fgebhart/smart_alarm/playground/light_up_leds.py

import sys
import os
sys.path.append(os.path.abspath("/home/pi/APA102_Pi"))
import colorschemes


numLEDs = 9

print('Rainbow Brightness 5of10')
myCycle = colorschemes.Rainbow(numLEDs=numLEDs, pauseValue=0.05, numStepsPerCycle = 255, numCycles = 2, globalBrightness=5)
myCycle.start()

print('Just plain white for 3 seconds')
myCycle = colorschemes.Solid(numLEDs=numLEDs, pauseValue=3, numStepsPerCycle = 1, numCycles = 1)
myCycle.start()
